jh442/run-type-keyboard/files/kicad/theRunner65.kicad_sch

## KiCad design files/kicad/theRunner65.kicad_sch (2023-05-05)

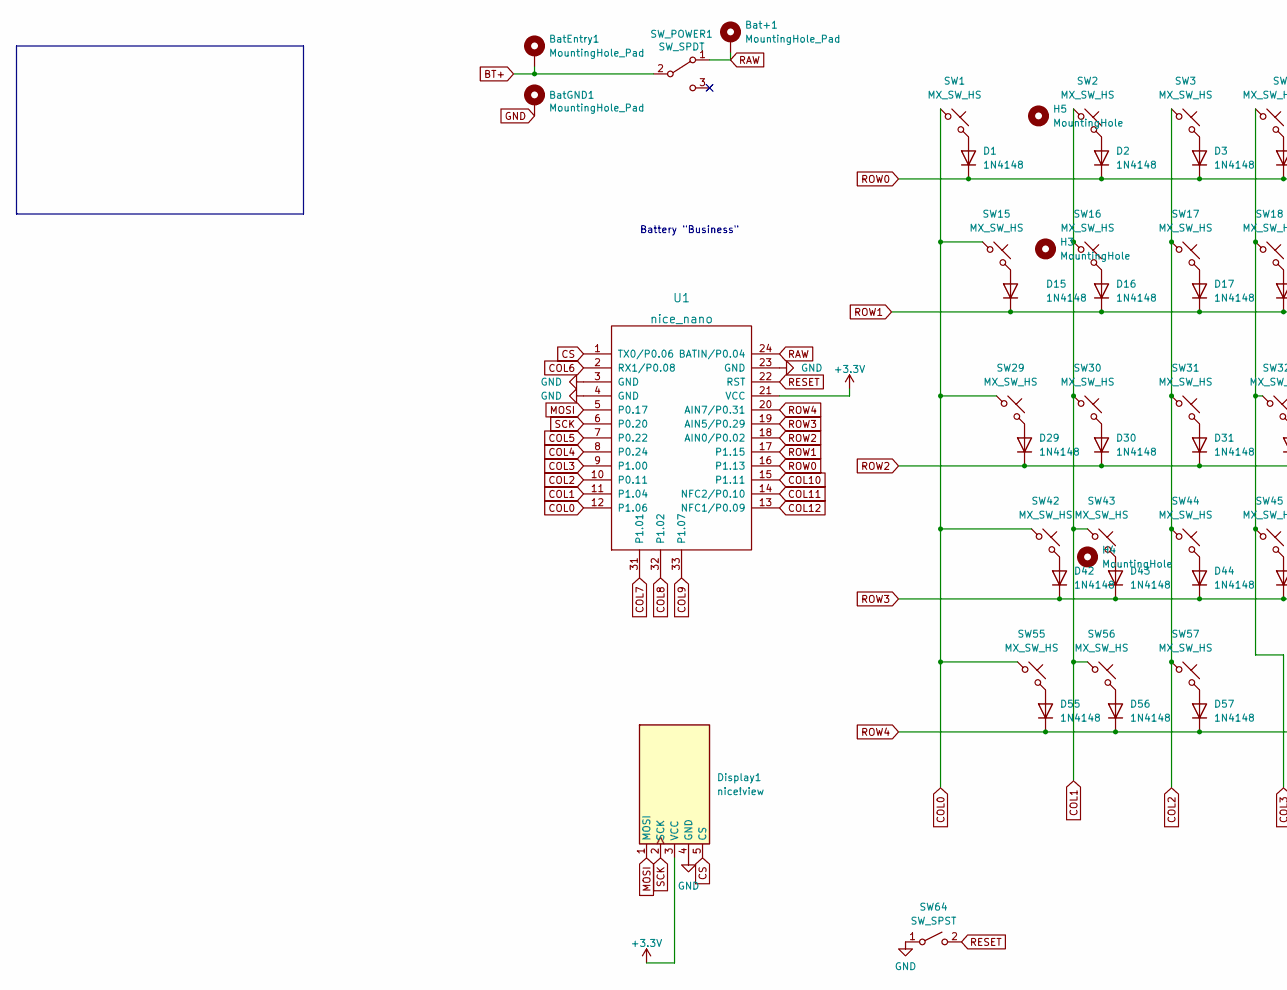
[picture p25: schematic theRunner65.kicad_sch, part in row 1, column 1]

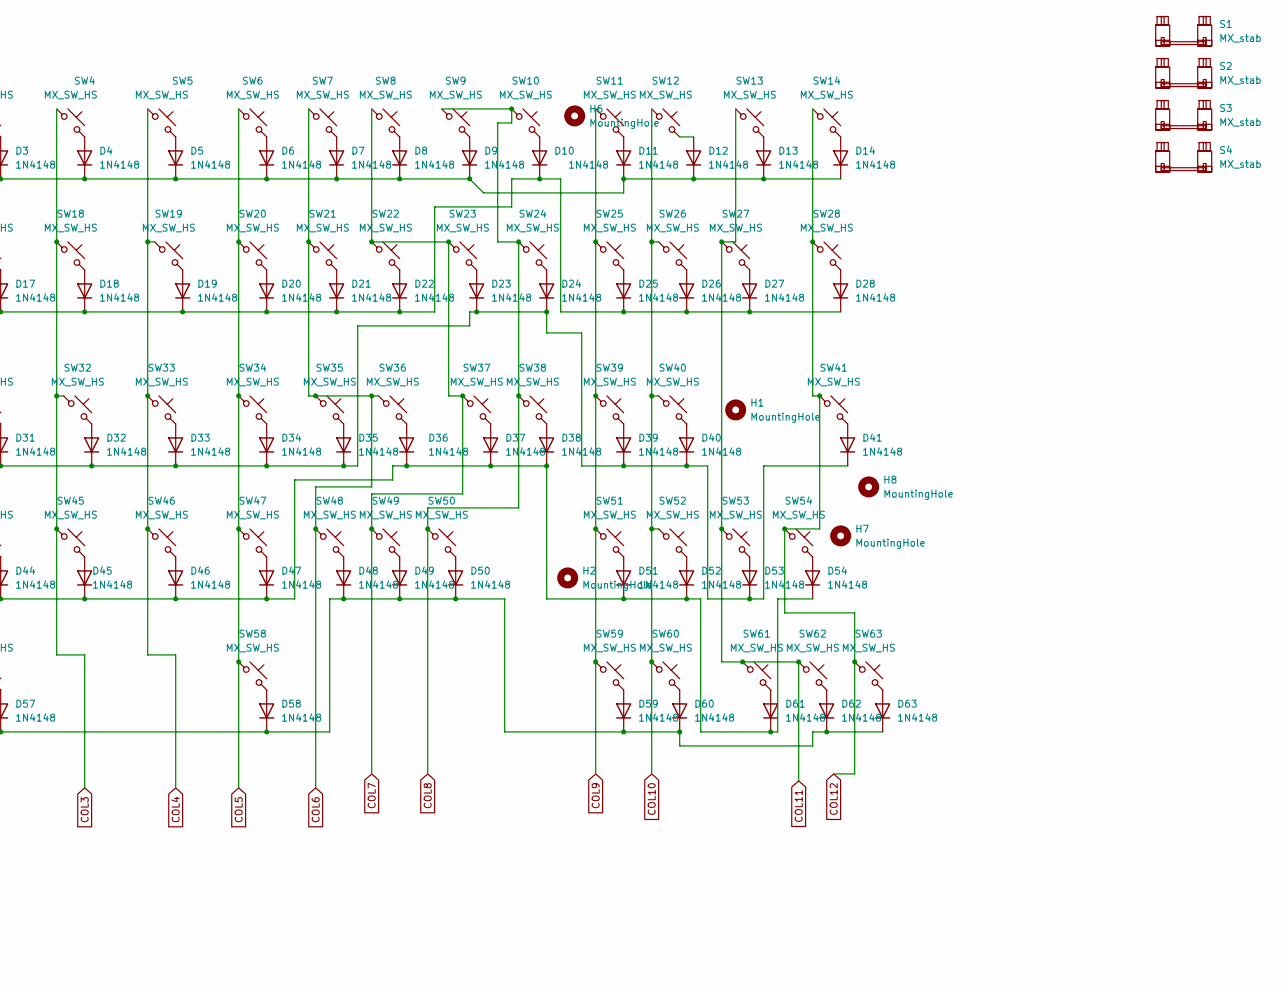
[picture p26: schematic theRunner65.kicad_sch, part in row 1, column 2]

Parts:
Bat+1: MountingHole_Pad; 1pin_Battery
BatEntry1: MountingHole_Pad; 1pin_Battery
BatGND1: MountingHole_Pad; 1pin_Battery
D1, D2, D3, D4, D5, D6, D7, D8, D9, D10, D11, D12, D13, D14, D15, D16, D17, D18, D19, D20, D21, D22, D23, D24, D25, D26, D27, D28, D29, D30, D31, D32, D33, D34, D35, D36, D37, D38, D39, D40, D41, D42, D43, D44, D45, D46, D47, D48, D49, D50, D51, D52, D53, D54, D55, D56, D57, D58, D59, D60, D61, D62, D63: 1N4148; D_DO-35_SOD27_P7.62mm_Horizontal
Display1: nice!view; nice_view
H1, H2, H3, H4: MountingHole; MountingHole_2.5mm_Pad
H5, H6, H7, H8: MountingHole; MountingHole_2.2mm_M2_Pad_Via
S1: MX_stab; STAB_MX_P_2u
S2, S3: MX_stab; STAB_MX_P_2.25u
S4: MX_stab; STAB_MX_P_6.25u
SW1, SW2, SW3, SW4, SW5, SW6, SW7, SW8, SW9, SW10, SW11, SW12, SW13, SW14, SW16, SW17, SW18, SW19, SW20, SW21, SW22, SW23, SW24, SW25, SW26, SW27, SW30, SW31, SW32, SW33, SW34, SW35, SW36, SW37, SW38, SW39, SW40, SW41, SW42, SW43, SW44, SW45, SW46, SW47, SW48, SW49, SW50, SW51, SW52, SW54, SW58, SW61, SW62, SW63: MX_SW_HS; SW_MX_HS_1u
SW15, SW28: MX_SW_HS; SW_MX_HS_1.5u
SW29, SW53: MX_SW_HS; SW_MX_HS_1.75u
SW55, SW56, SW57, SW59, SW60: MX_SW_HS; SW_MX_HS_1.25u
SW64: SW_SPST; SW_PUSH_6mm
SW_POWER1: SW_SPDT; SPDT_C128955
U1: nice_nano

Connections:
+3.3V: Display1.3 (VCC), U1.21 (VCC)
BT+: BatEntry1.1, SW_POWER1.2 (B)
COL0: SW1.1, SW15.1, SW29.1, SW42.1, SW55.1, U1.12 (P1.06)
COL1: SW2.1, SW16.1, SW30.1, SW43.1, SW56.1, U1.11 (P1.04)
COL2: SW3.1, SW17.1, SW31.1, SW44.1, SW57.1, U1.10 (P0.11)
COL3: SW4.1, SW18.1, SW32.1, SW45.1, U1.9 (P1.00)
COL4: SW5.1, SW19.1, SW33.1, SW46.1, U1.8 (P0.24)
COL5: SW6.1, SW20.1, SW34.1, SW47.1, SW58.1, U1.7 (P0.22)
COL6: SW7.1, SW21.1, SW35.1, SW36.1, SW48.1, U1.2 (RX1/P0.08)
COL7: SW8.1, SW22.1, SW23.1, SW37.1, SW49.1, U1.31 (P1.01)
COL8: SW9.1, SW10.1, SW24.1, SW38.1, SW50.1, U1.32 (P1.02)
COL9: SW11.1, SW25.1, SW39.1, SW51.1, SW59.1, U1.33 (P1.07)
COL10: SW12.1, SW26.1, SW40.1, SW52.1, SW60.1, U1.15 (P1.11)
COL11: SW13.1, SW27.1, SW53.1, SW61.1, SW62.1, U1.14 (NFC2/P0.10)
COL12: SW14.1, SW28.1, SW41.1, SW54.1, SW63.1, U1.13 (NFC1/P0.09)
CS: Display1.5 (CS), U1.1 (TX0/P0.06)
GND: BatGND1.1, Display1.4 (GND), SW64.1 (A), U1.3 (GND), U1.4 (GND), U1.23 (GND)
MOSI: Display1.1 (MOSI), U1.5 (P0.17)
unnamed: D1.2 (A), SW1.2
unnamed: D2.2 (A), SW2.2
unnamed: D3.2 (A), SW3.2
unnamed: D4.2 (A), SW4.2
unnamed: D5.2 (A), SW5.2
unnamed: D6.2 (A), SW6.2
unnamed: D7.2 (A), SW7.2
unnamed: D8.2 (A), SW8.2
unnamed: D9.2 (A), SW9.2
unnamed: D10.2 (A), SW10.2
unnamed: D11.2 (A), SW11.2
unnamed: D12.2 (A), SW12.2
unnamed: D13.2 (A), SW13.2
unnamed: D14.2 (A), SW14.2
unnamed: D15.2 (A), SW15.2
unnamed: D16.2 (A), SW16.2
unnamed: D17.2 (A), SW17.2
unnamed: D18.2 (A), SW18.2
unnamed: D19.2 (A), SW19.2
unnamed: D20.2 (A), SW20.2
unnamed: D21.2 (A), SW21.2
unnamed: D22.2 (A), SW22.2
unnamed: D23.2 (A), SW23.2
unnamed: D24.2 (A), SW24.2
unnamed: D25.2 (A), SW25.2
unnamed: D26.2 (A), SW26.2
unnamed: D27.2 (A), SW27.2
unnamed: D28.2 (A), SW28.2
unnamed: D29.2 (A), SW29.2
unnamed: D30.2 (A), SW30.2
unnamed: D31.2 (A), SW31.2
unnamed: D32.2 (A), SW32.2
unnamed: D33.2 (A), SW33.2
unnamed: D34.2 (A), SW34.2
unnamed: D35.2 (A), SW35.2
unnamed: D36.2 (A), SW36.2
unnamed: D37.2 (A), SW37.2
unnamed: D38.2 (A), SW38.2
unnamed: D39.2 (A), SW39.2
unnamed: D40.2 (A), SW40.2
unnamed: D41.2 (A), SW41.2
unnamed: D42.2 (A), SW42.2
unnamed: D43.2 (A), SW43.2
unnamed: D44.2 (A), SW44.2
unnamed: D45.2 (A), SW45.2
unnamed: D46.2 (A), SW46.2
unnamed: D47.2 (A), SW47.2
unnamed: D48.2 (A), SW48.2
unnamed: D49.2 (A), SW49.2
unnamed: D50.2 (A), SW50.2
unnamed: D51.2 (A), SW51.2
unnamed: D52.2 (A), SW52.2
unnamed: D53.2 (A), SW53.2
unnamed: D54.2 (A), SW54.2
unnamed: D55.2 (A), SW55.2
unnamed: D56.2 (A), SW56.2
unnamed: D57.2 (A), SW57.2
unnamed: D58.2 (A), SW58.2
unnamed: D59.2 (A), SW59.2
unnamed: D60.2 (A), SW60.2
unnamed: D61.2 (A), SW61.2
unnamed: D62.2 (A), SW62.2
unnamed: D63.2 (A), SW63.2
RAW: Bat+1.1, SW_POWER1.1 (A), U1.24 (BATIN/P0.04)
RESET: SW64.2 (B), U1.22 (RST)
ROW0: D1.1 (K), D2.1 (K), D3.1 (K), D4.1 (K), D5.1 (K), D6.1 (K), D7.1 (K), D8.1 (K), D9.1 (K), D11.1 (K), D12.1 (K), D13.1 (K), D14.1 (K), U1.16 (P1.13)
ROW1: D10.1 (K), D15.1 (K), D16.1 (K), D17.1 (K), D18.1 (K), D19.1 (K), D20.1 (K), D21.1 (K), D22.1 (K), D25.1 (K), D26.1 (K), D27.1 (K), D28.1 (K), U1.17 (P1.15)
ROW2: D23.1 (K), D24.1 (K), D29.1 (K), D30.1 (K), D31.1 (K), D32.1 (K), D33.1 (K), D34.1 (K), D35.1 (K), D39.1 (K), D40.1 (K), D41.1 (K), D53.1 (K), U1.18 (AIN0/P0.02)
ROW3: D36.1 (K), D37.1 (K), D38.1 (K), D42.1 (K), D43.1 (K), D44.1 (K), D45.1 (K), D46.1 (K), D47.1 (K), D51.1 (K), D52.1 (K), D54.1 (K), D61.1 (K), U1.19 (AIN5/P0.29)
ROW4: D48.1 (K), D49.1 (K), D50.1 (K), D55.1 (K), D56.1 (K), D57.1 (K), D58.1 (K), D59.1 (K), D60.1 (K), D62.1 (K), D63.1 (K), U1.20 (AIN7/P0.31)
SCK: Display1.2 (SCK), U1.6 (P0.20)

Notes on the sheet:
Battery "Business"
